vaarnaa/ProtopajaProjekti/Kotisivu/Kuvat/aleksi_2.jpg

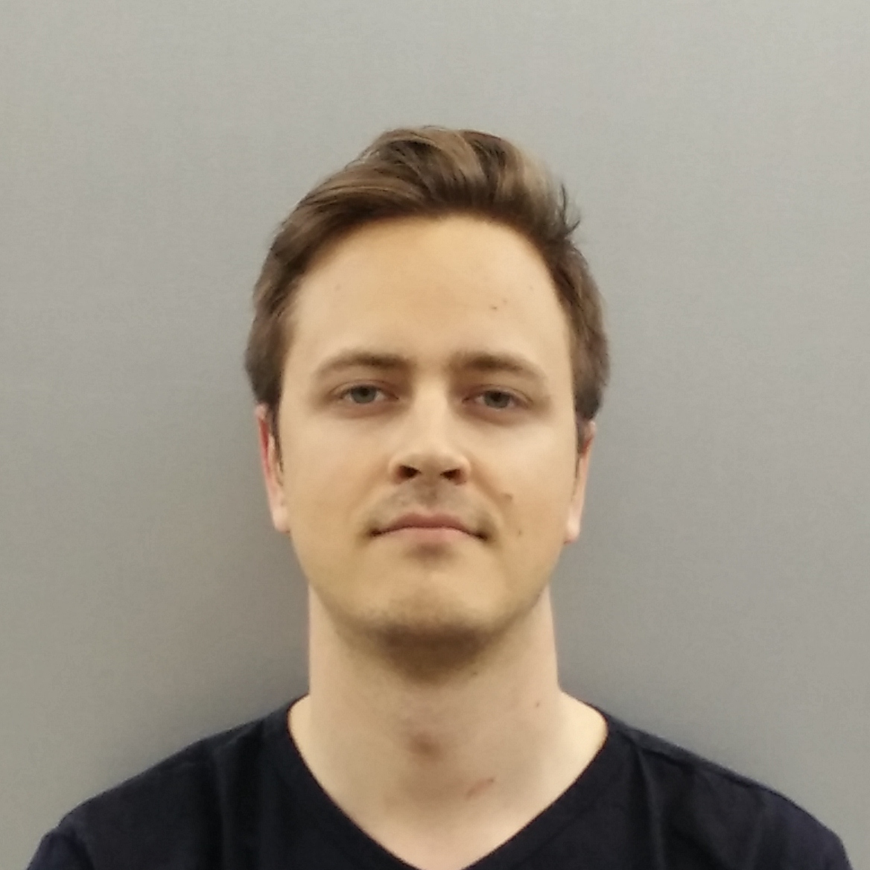
Kotisivu/Kuvat/aleksi_2.jpg
