vaarnaa/ProtopajaProjekti/Kotisivu/Kuvat/joel.jpg

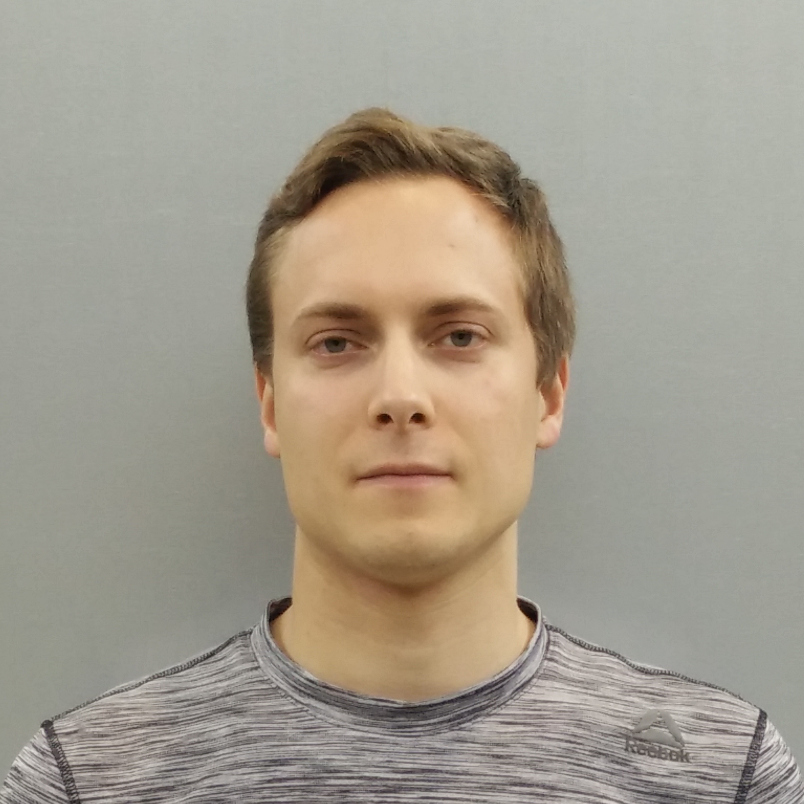
Kotisivu/Kuvat/joel.jpg
