vaarnaa/ProtopajaProjekti/Kotisivu/Kuvat/koodi.JPG

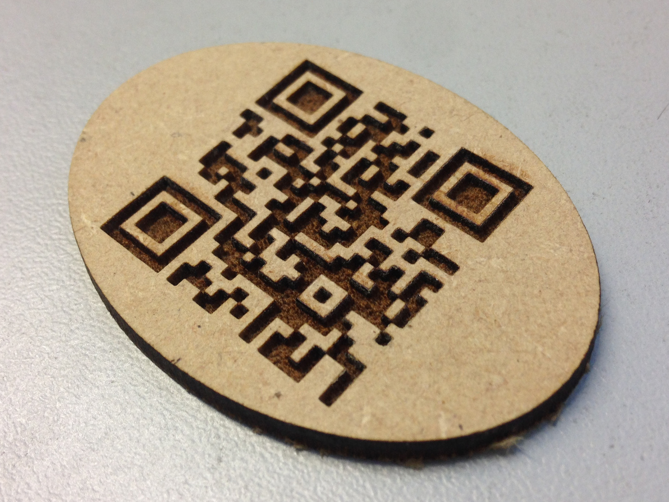
Kotisivu/Kuvat/koodi.JPG
