vaarnaa/ProtopajaProjekti/Kotisivu/Kuvat/kotelo_sisalta.JPG

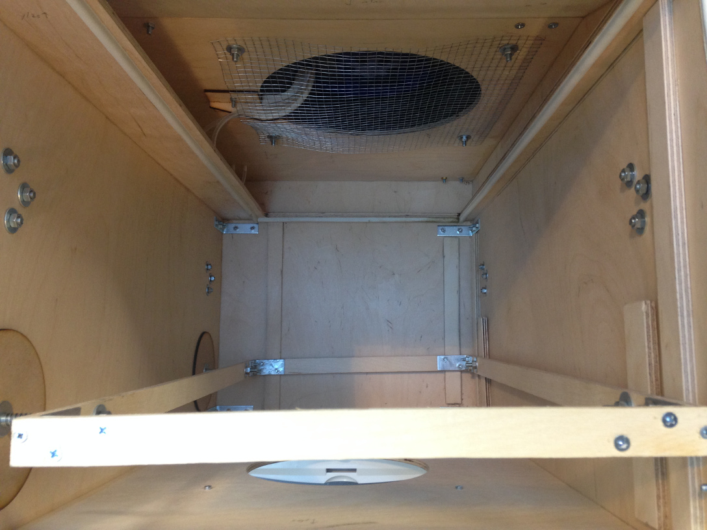
Kotisivu/Kuvat/kotelo_sisalta.JPG
