vaarnaa/ProtopajaProjekti/Kotisivu/Kuvat/ledit.jpg

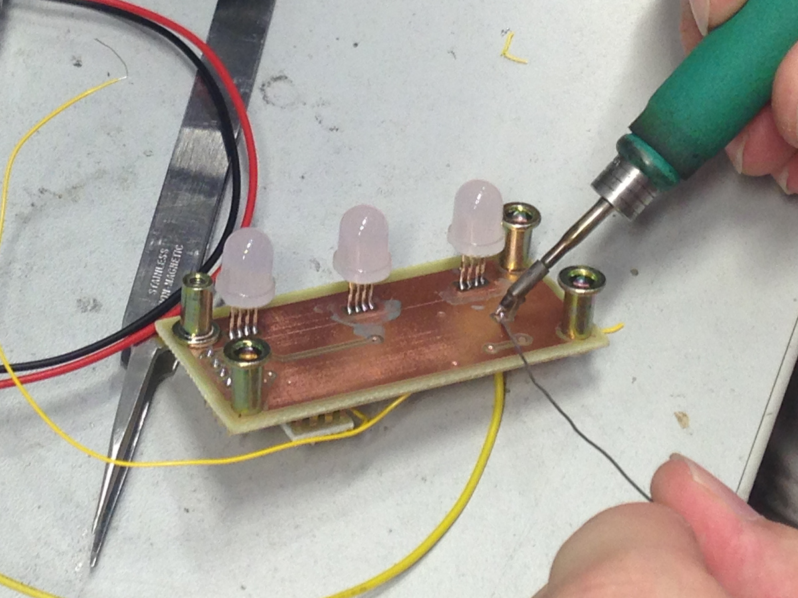
Kotisivu/Kuvat/ledit.jpg
