vaarnaa/ProtopajaProjekti/Kotisivu/Kuvat/miika_2.jpg

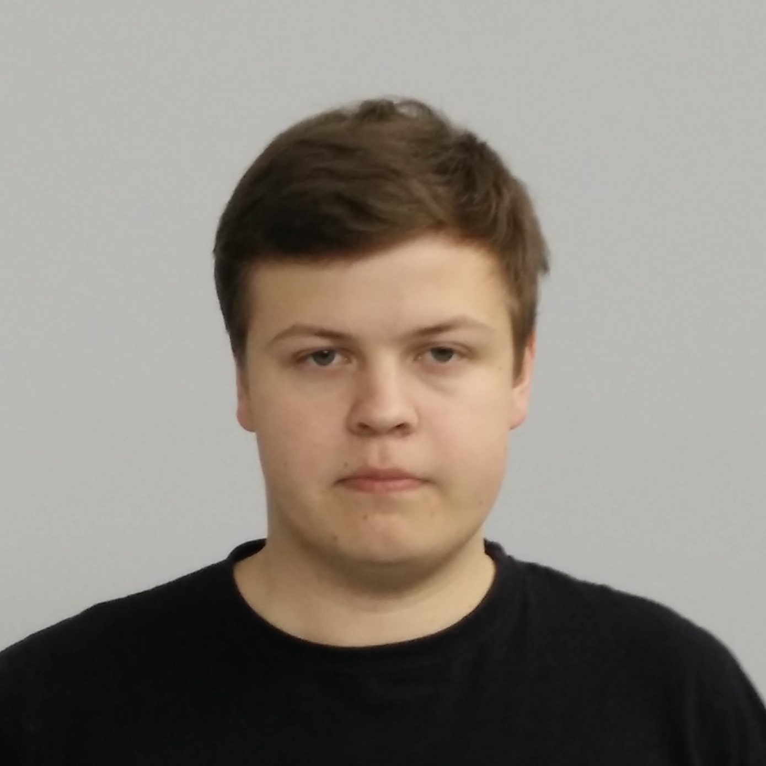
Kotisivu/Kuvat/miika_2.jpg
