vaarnaa/ProtopajaProjekti/Kotisivu/Kuvat/PID_diagram_2.png

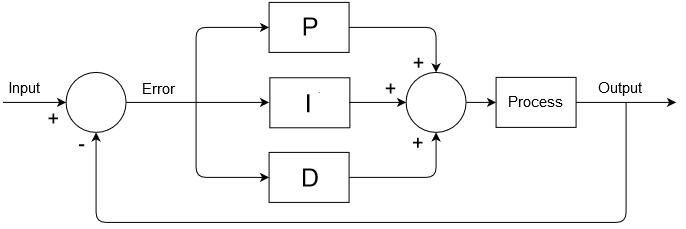
Kotisivu/Kuvat/PID_diagram_2.png
