vaarnaa/ProtopajaProjekti/Kotisivu/Kuvat/PID_diagrammi.png

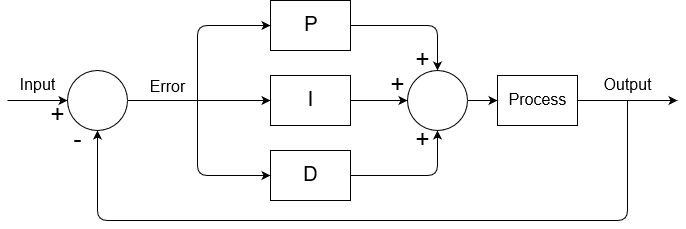
Kotisivu/Kuvat/PID_diagrammi.png
