vaarnaa/ProtopajaProjekti/Kotisivu/Kuvat/piiri_kylpy.JPG

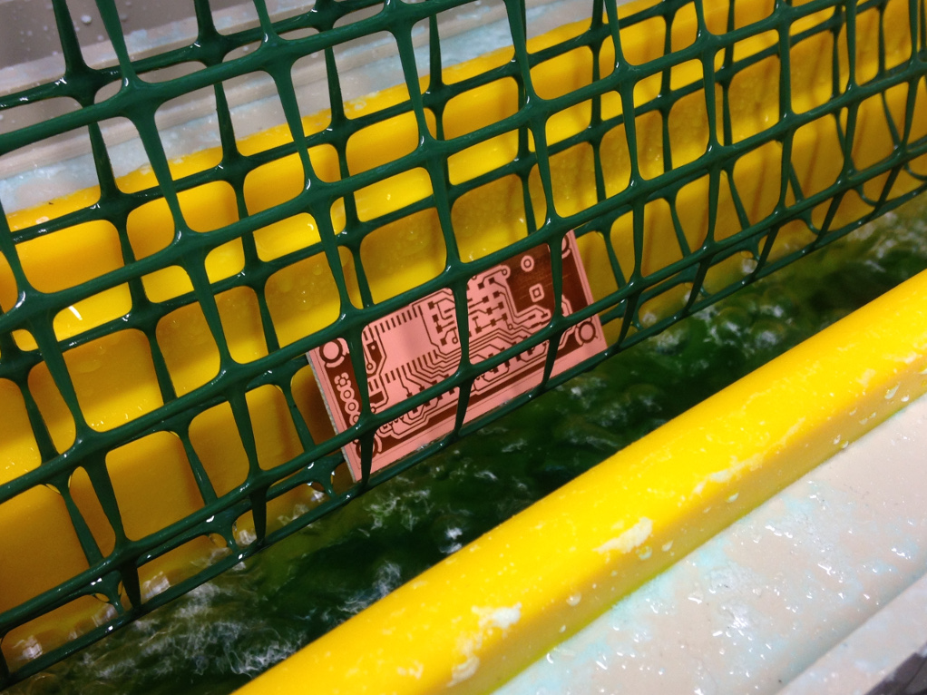
Kotisivu/Kuvat/piiri_kylpy.JPG
