vaarnaa/ProtopajaProjekti/Kotisivu/Kuvat/piirilevy - Copy.jpg

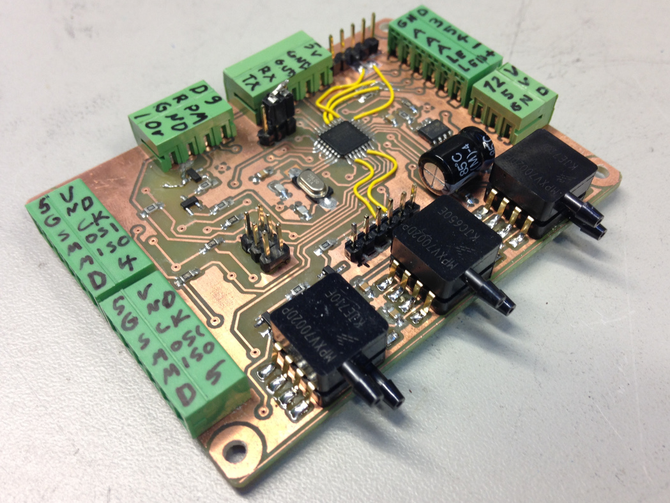
Kotisivu/Kuvat/piirilevy - Copy.jpg
