vaarnaa/ProtopajaProjekti/Kotisivu/Kuvat/piirilevy_compressed.png

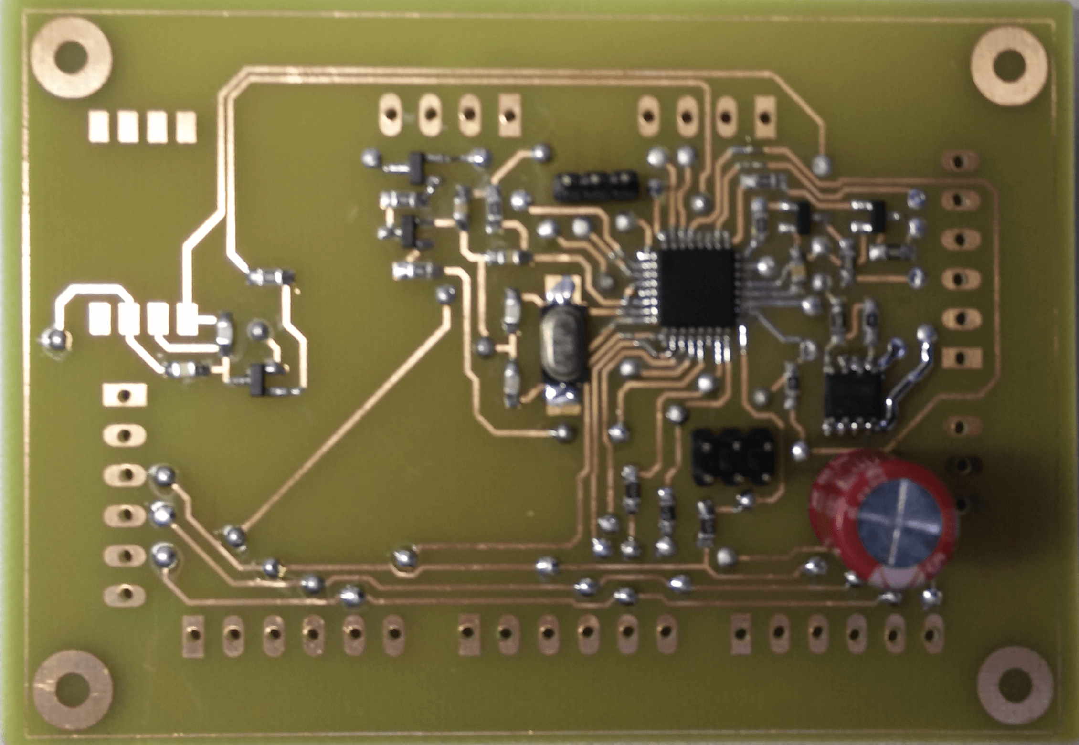
Kotisivu/Kuvat/piirilevy_compressed.png
